igor-k07/FE-2023-Inside/src/load_final.PNG

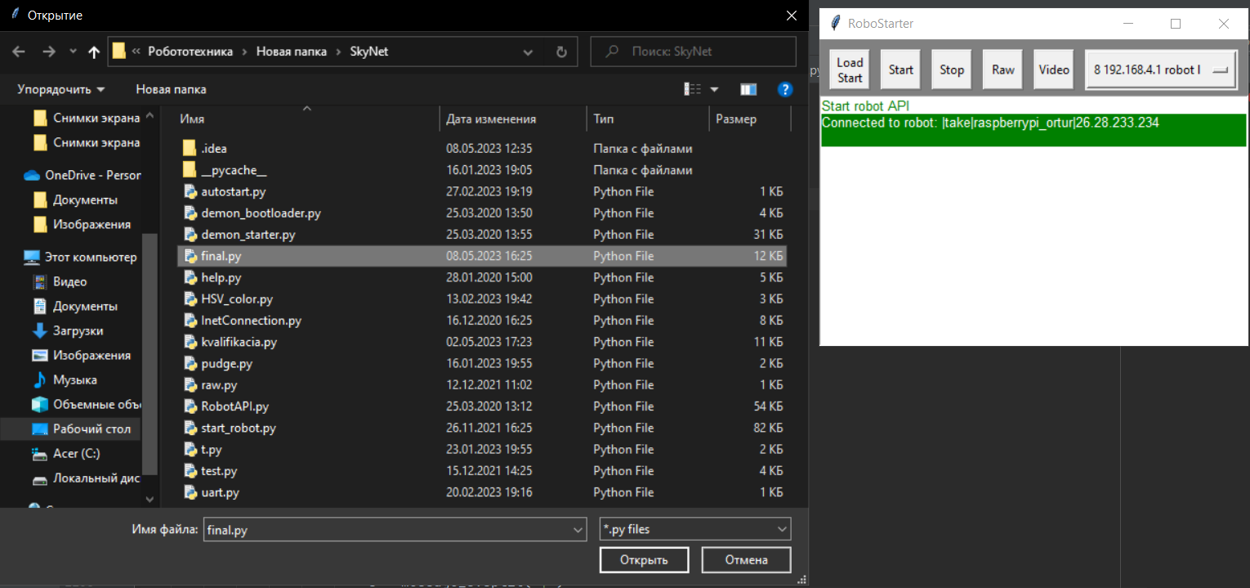
src/load_final.PNG
