igor-k07/FE-2023-Inside/Фото команды/Неофициальная фотография.jpeg

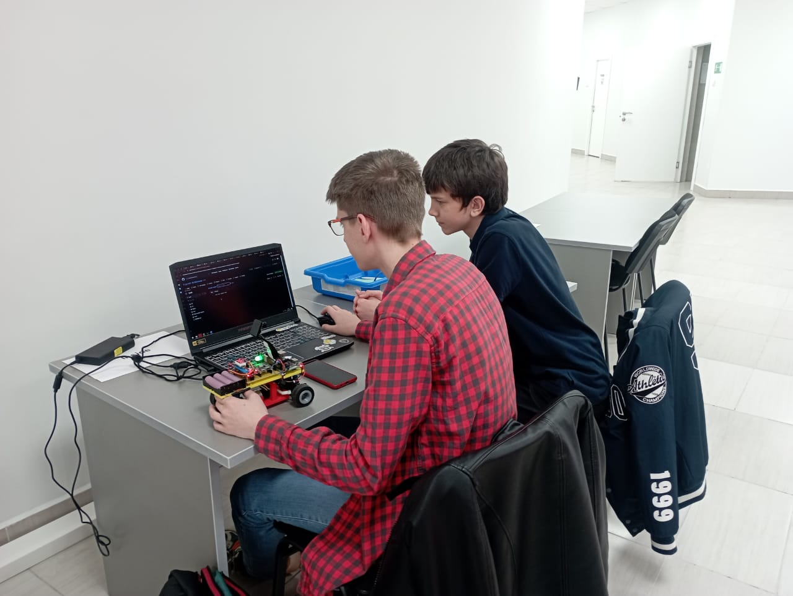
Фото команды/Неофициальная фотография.jpeg
