igor-k07/FE-2023-Inside/Фото робота/Вид снизу.jpeg

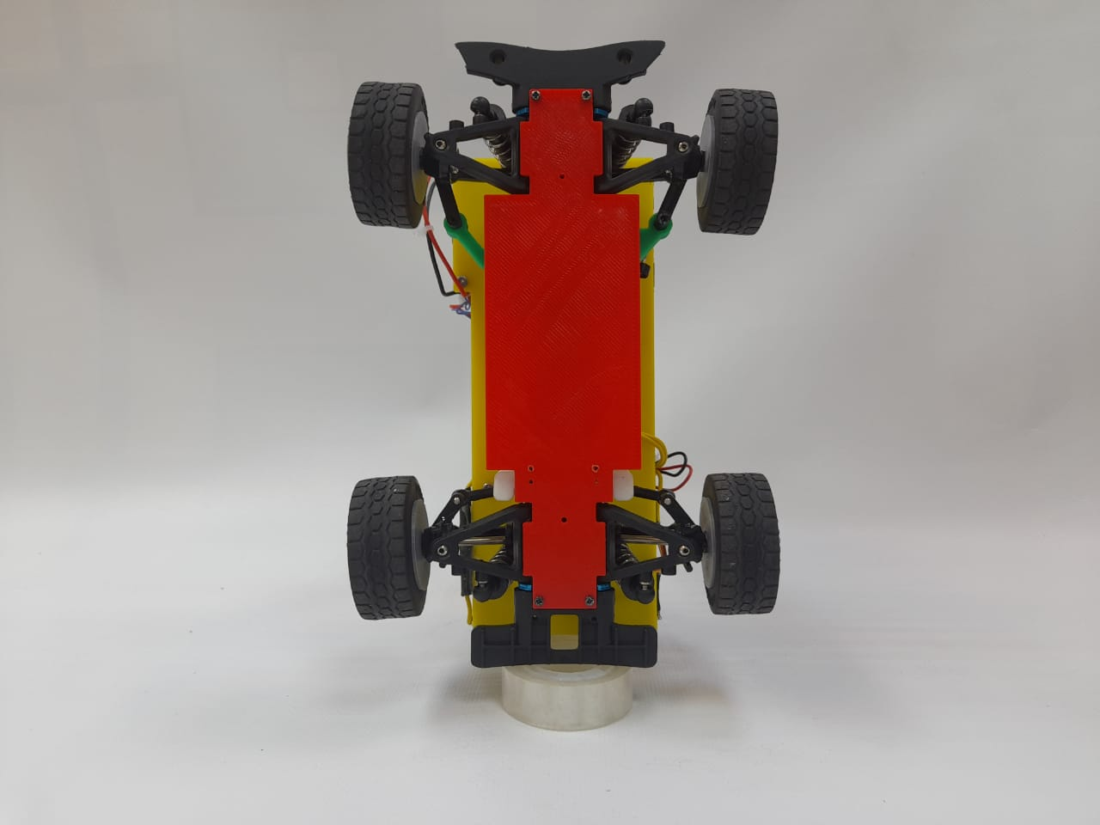
Фото робота/Вид снизу.jpeg
